kripthor/UberHid/firmware/UberHID-ESPUSB/Config.h

#ifndef UHConfig_h
#define UHConfig_h

#define WIFISSID        "UBERHID"
#define WIFIPASS        "uberidiota"
#define WIFICHANNEL     7
#define WIFISSIDHIDDEN  0 // 0 for not hidden

#define OTANAME         "uberhid-iota"
#define OTAPASS         "uberidiota"


// DO NOT CHANGE!
#define RXPINLEO        2
#define TXPINLEO        4


#endif
