kripthor/UberHid/firmware/UberHID-ESPUSB/Ota.h

/*
  Ota.h
  OTA related stuff
  Needs refactoring, a bunch of static functions in a .h sucks.
  Created by kripthor, October 2019
*/

#ifndef UHOta_h
#define UHOta_h

void startOTA() { // Start the OTA service
  ArduinoOTA.setHostname(OTANAME);
  ArduinoOTA.setPassword(OTAPASS);

  ArduinoOTA.onStart([]() {
    Serial.println("Start OTA");
  });
  ArduinoOTA.onEnd([]() {
    Serial.println("\r\nEnd OTA");
  });
  ArduinoOTA.onProgress([](unsigned int progress, unsigned int total) {
    Serial.printf("Progress OTA: %u%%\r", (progress / (total / 100)));
  });
  ArduinoOTA.onError([](ota_error_t error) {
    Serial.printf("Error[%u]: ", error);
    if (error == OTA_AUTH_ERROR) Serial.println("Auth Failed");
    else if (error == OTA_BEGIN_ERROR) Serial.println("Begin Failed");
    else if (error == OTA_CONNECT_ERROR) Serial.println("Connect Failed");
    else if (error == OTA_RECEIVE_ERROR) Serial.println("Receive Failed");
    else if (error == OTA_END_ERROR) Serial.println("End Failed");
  });
  ArduinoOTA.begin();
  Serial.println("OTA ready\r\n");
}


#endif
